Ratamuse/Open_beehive_scale_V0.2/Electronique balance/HTIT-WSL_V3.png

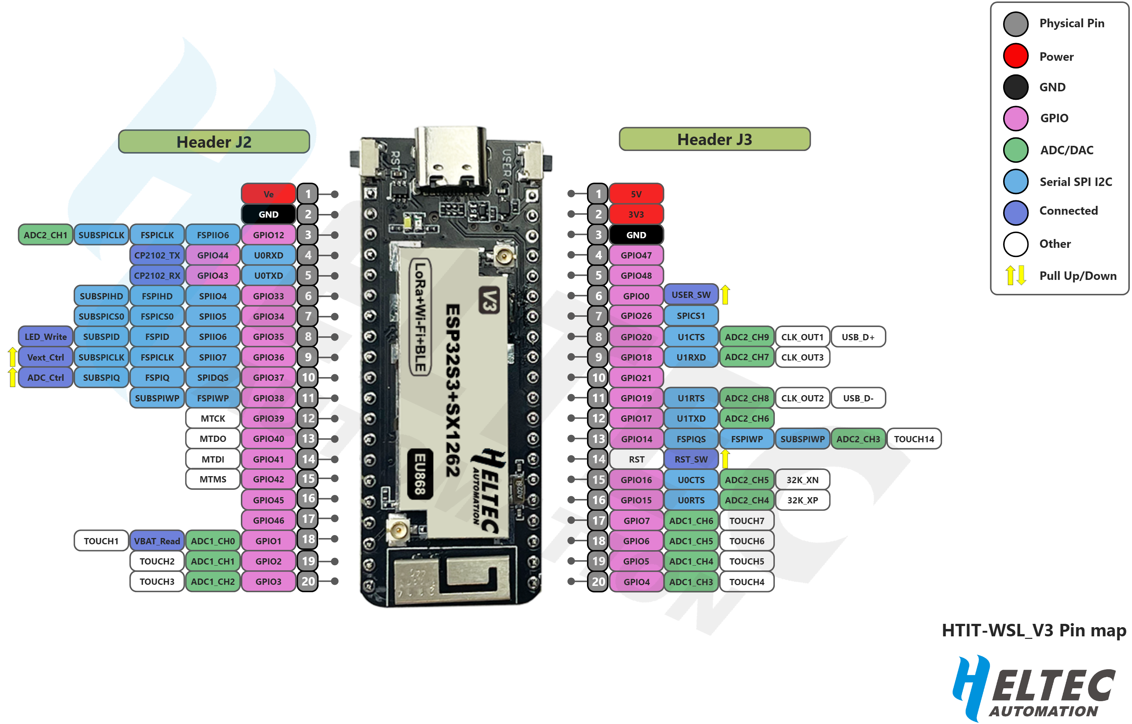
Electronique balance/HTIT-WSL_V3.png
