Ratamuse/Open_beehive_scale_V0.2/Electronique balance/3D/AO3400.stp

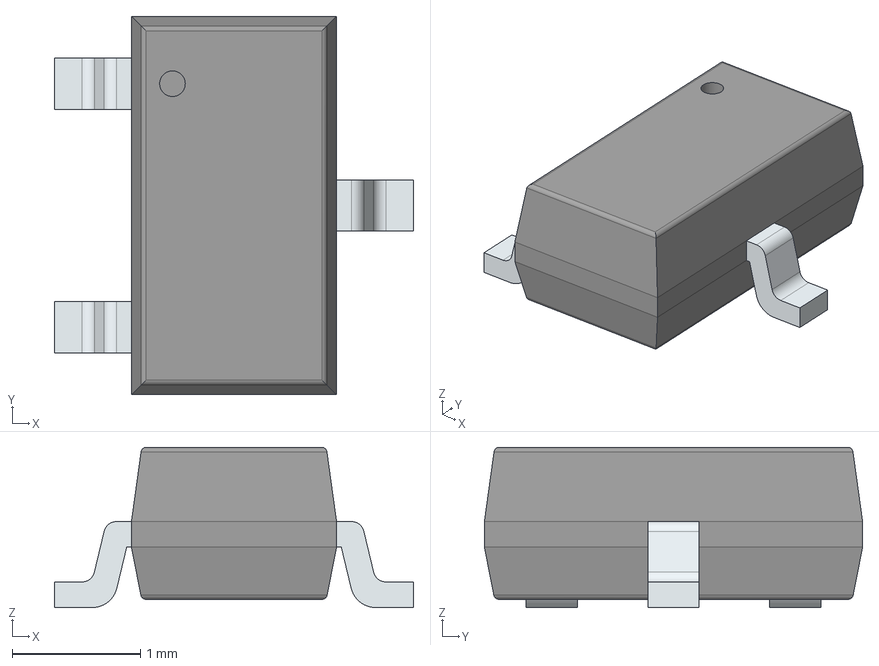
[picture p21: CAD file, 2022-06-07]
Electronique balance/3D/AO3400.stp
2.80 x 2.95 x 1.25 mm
PinsArrayL
FilletPinR
