Ratamuse/Open_beehive_scale_V0.2/Electronique balance/3D/FS8205.stp

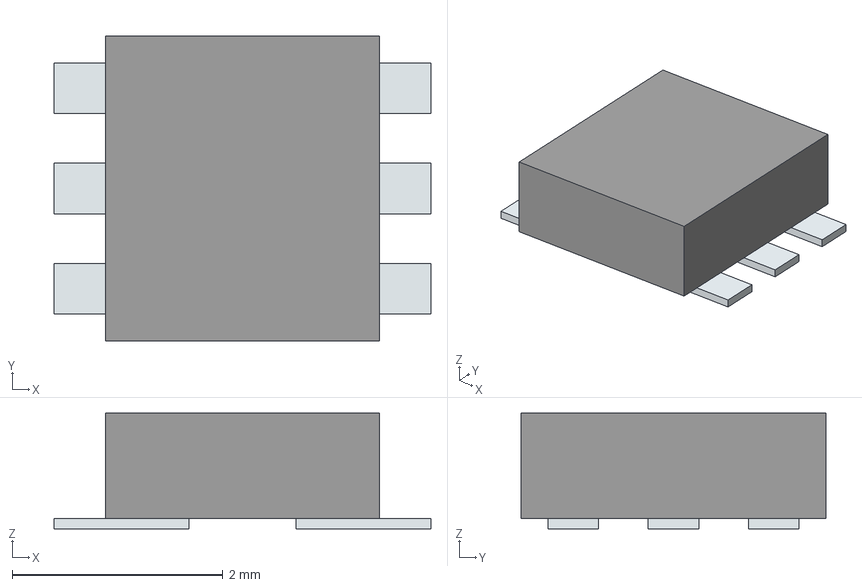
[picture p22: CAD file, 2022-06-07]
Electronique balance/3D/FS8205.stp
3.58 x 2.90 x 1.10 mm
Pins
