Ratamuse/Open_beehive_scale_V0.2/Electronique balance/3D/MMBT4403.stp

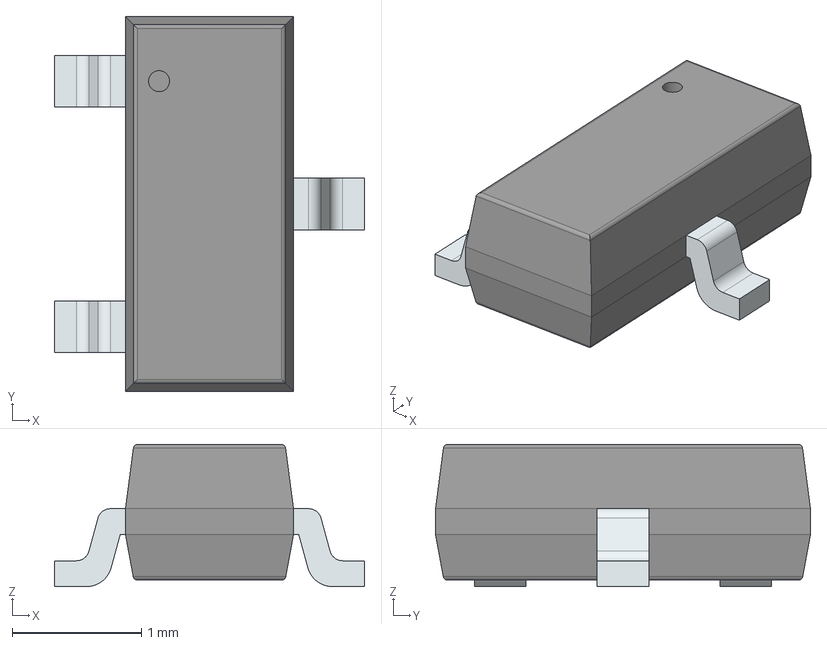
[picture p23: CAD file, 2022-06-07]
Electronique balance/3D/MMBT4403.stp
2.40 x 2.90 x 1.10 mm
PinsArrayL
FilletPinR
