Ratamuse/Open_beehive_scale_V0.2/Electronique balance/3D/B3S_100[].step

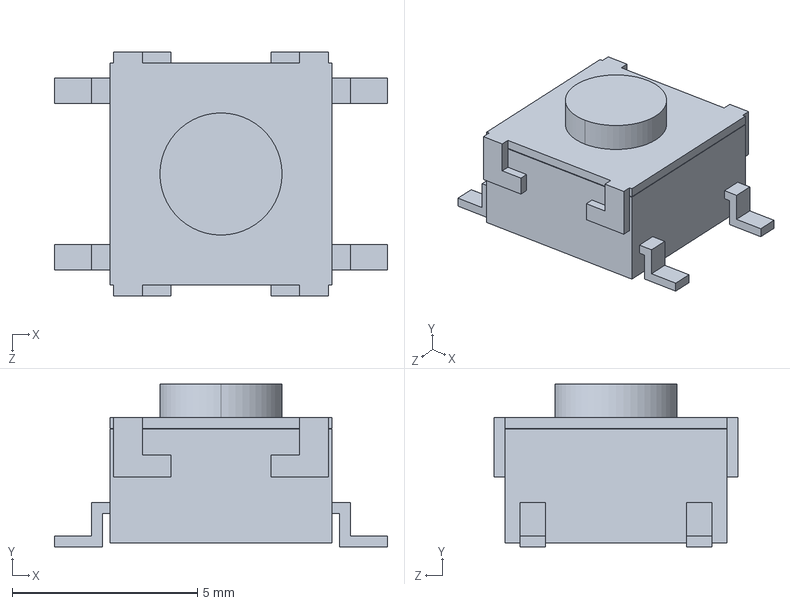
[picture p25: CAD file, 2022-06-07]
Electronique balance/3D/B3S_100[].step
9.00 x 4.40 x 6.60 mm
