Ratamuse/Open_beehive_scale_V0.2/Electronique balance/3D/SP1003-01DTG.stp

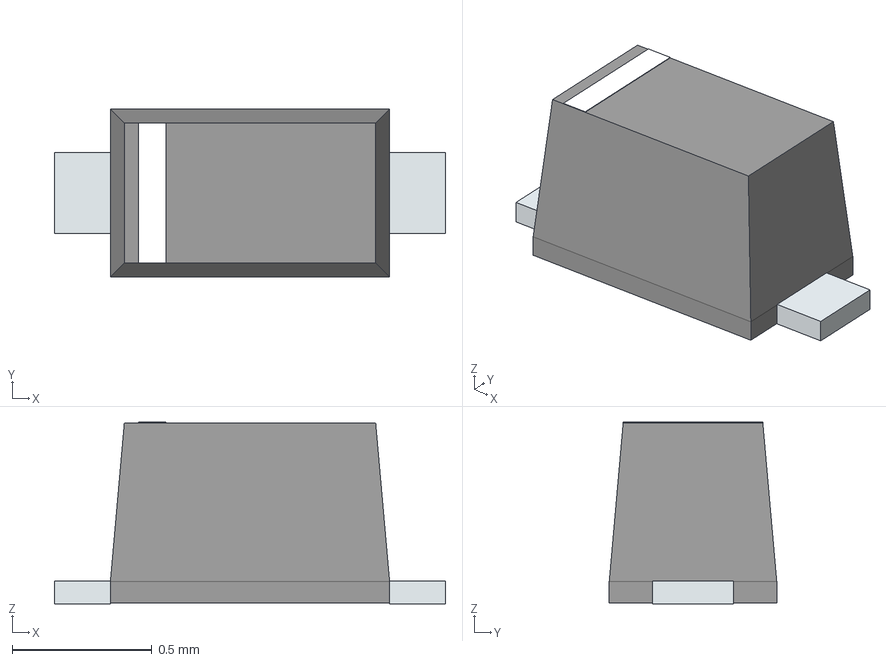
[picture p26: CAD file, 2022-06-07]
Electronique balance/3D/SP1003-01DTG.stp
1.40 x 0.6 x 0.65 mm
PinKIdent
PinK
PinA
