Ratamuse/Open_beehive_scale_V0.2/Electronique balance/3D/B4B-PH-SM4-TB.STEP

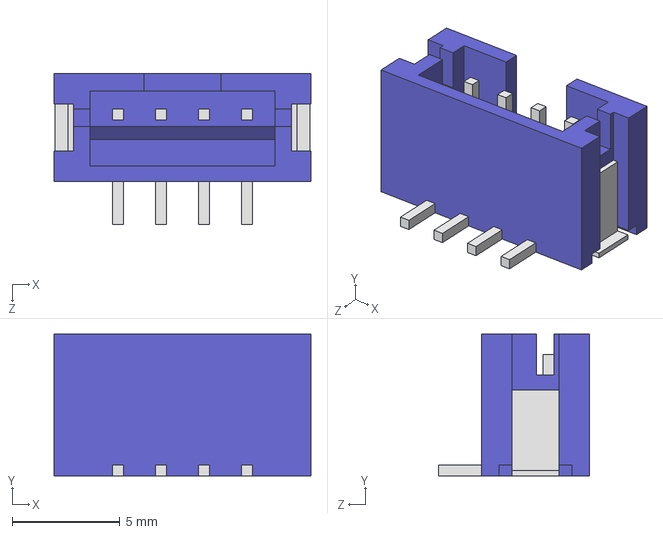
[picture p27: CAD file, 2022-06-07]
Electronique balance/3D/B4B-PH-SM4-TB.STEP
12.0 x 6.60 x 7.00 mm
