Ratamuse/Open_beehive_scale_V0.2/Electronique balance/3D/SdCard.stp

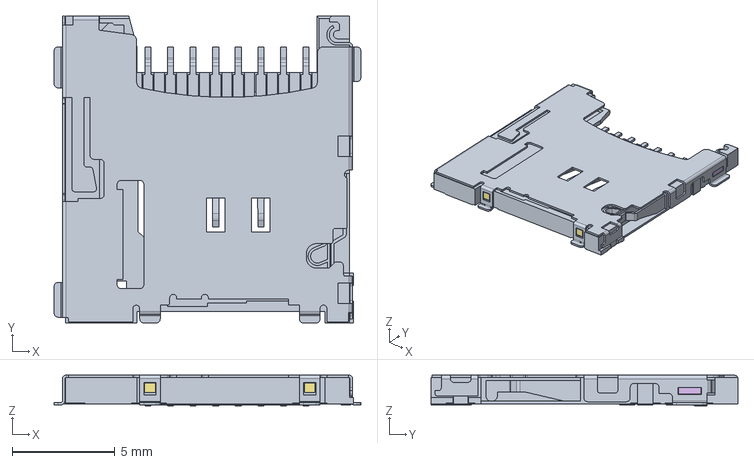
[picture p28: CAD file, 2022-06-07]
Electronique balance/3D/SdCard.stp
14.9 x 14.9 x 1.50 mm
