Ratamuse/Open_beehive_scale_V0.2/Electronique balance/3D/B2B-PH-K-S.STEP

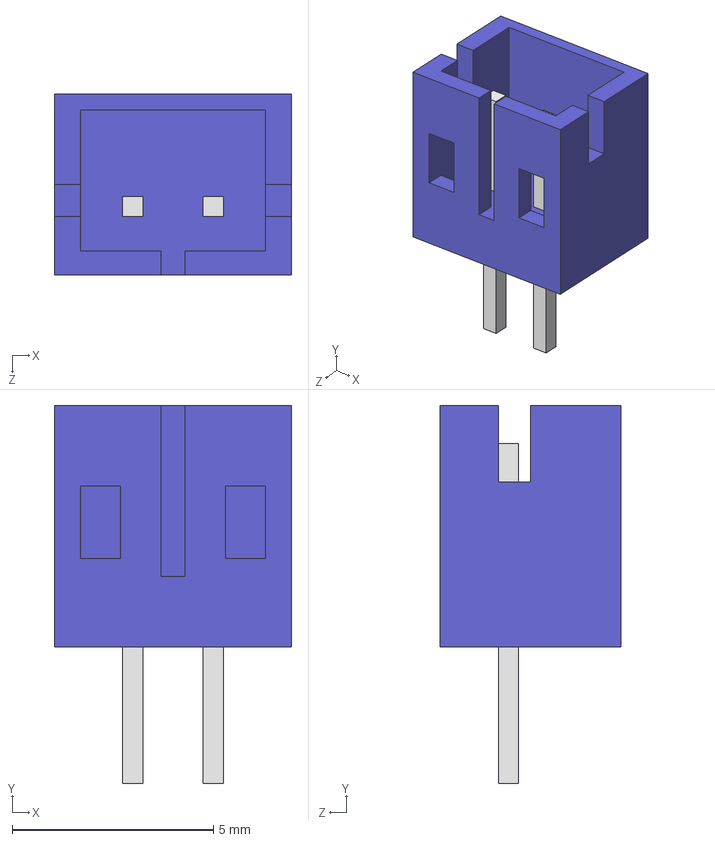
[picture p29: CAD file, 2022-06-07]
Electronique balance/3D/B2B-PH-K-S.STEP
5.90 x 9.40 x 4.50 mm
