Ratamuse/Open_beehive_scale_V0.2/Electronique balance/3D/HTSB-M3-8-5,5-1.STEP

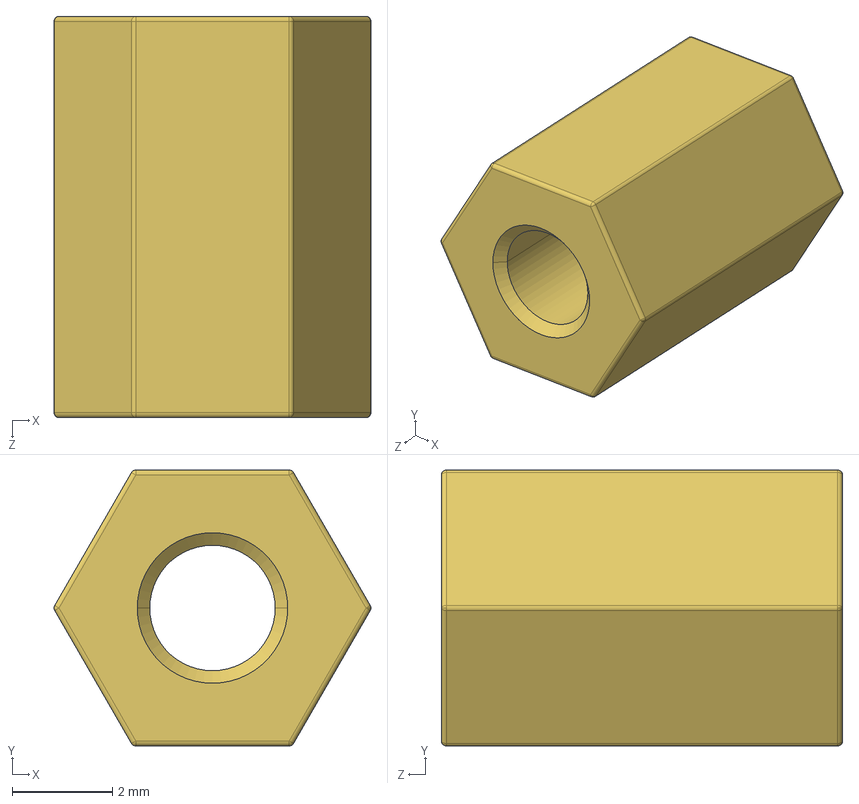
[picture p30: CAD file, 2022-06-07]
Electronique balance/3D/HTSB-M3-8-5,5-1.STEP
6.32 x 5.50 x 8.00 mm
