Ratamuse/Open_beehive_scale_V0.2/Electronique balance/3D/CN3791.stp

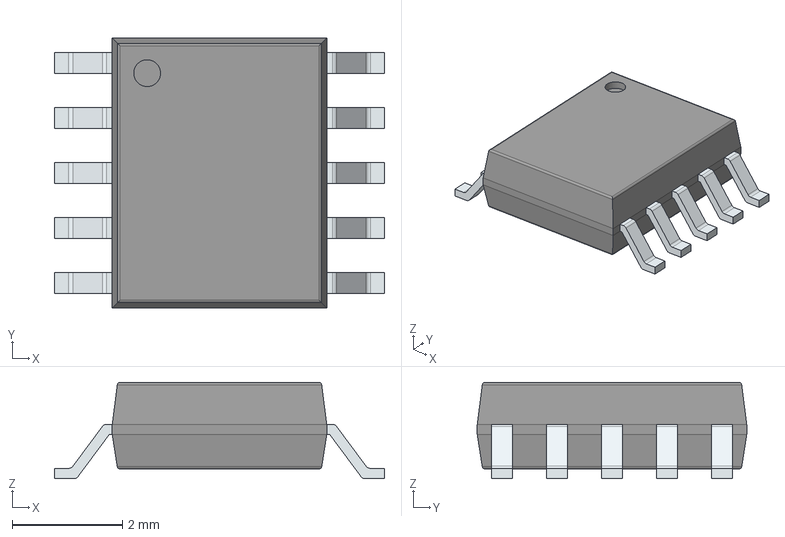
[picture p31: CAD file, 2022-06-07]
Electronique balance/3D/CN3791.stp
6.00 x 4.90 x 1.75 mm
PinsArrayLR
