Ratamuse/Open_beehive_scale_V0.2/Electronique balance/3D/PBS-14R.step

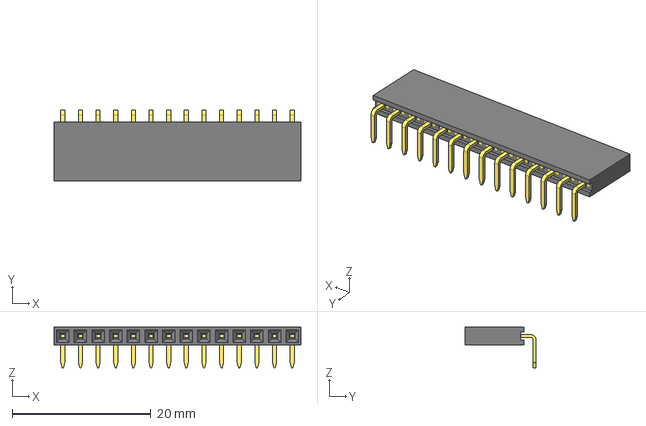
[picture p32: CAD file, 2022-06-07]
Electronique balance/3D/PBS-14R.step
35.6 x 10.2 x 5.84 mm
