Ratamuse/Open_beehive_scale_V0.2/Electronique balance/3D/FS8205A.stp

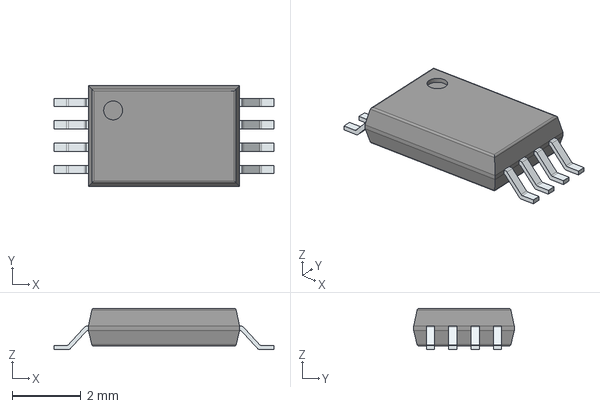
[picture p33: CAD file, 2022-06-07]
Electronique balance/3D/FS8205A.stp
6.40 x 2.93 x 1.20 mm
PinsArrayLR
