Ratamuse/Open_beehive_scale_V0.2/Electronique balance/3D/SHT41-AD1B-R3.stp

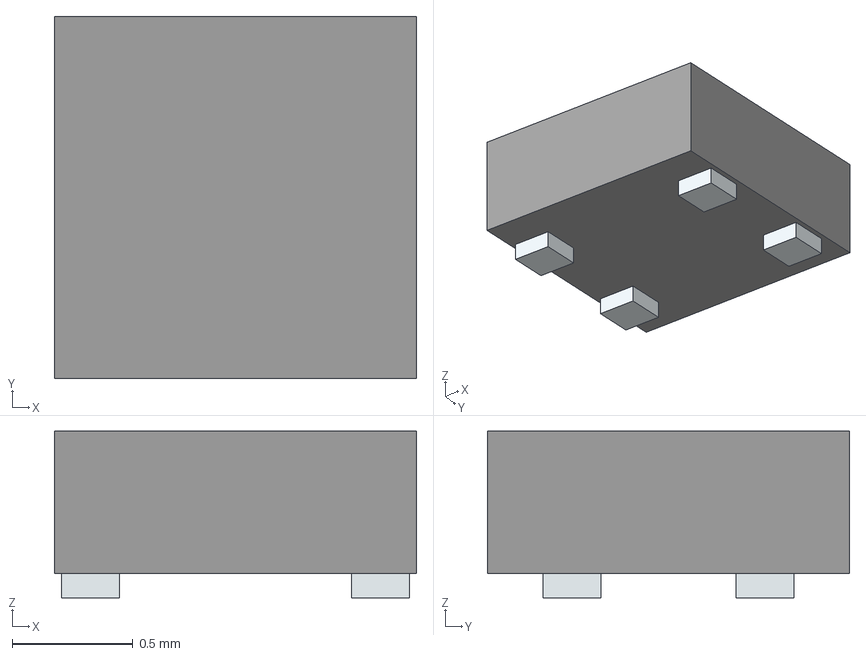
[picture p34: CAD file, 2022-06-07]
Electronique balance/3D/SHT41-AD1B-R3.stp
1.50 x 1.50 x 0.69 mm
Pins
