Ratamuse/Open_beehive_scale_V0.2/Electronique balance/3D/RB231X2.stp

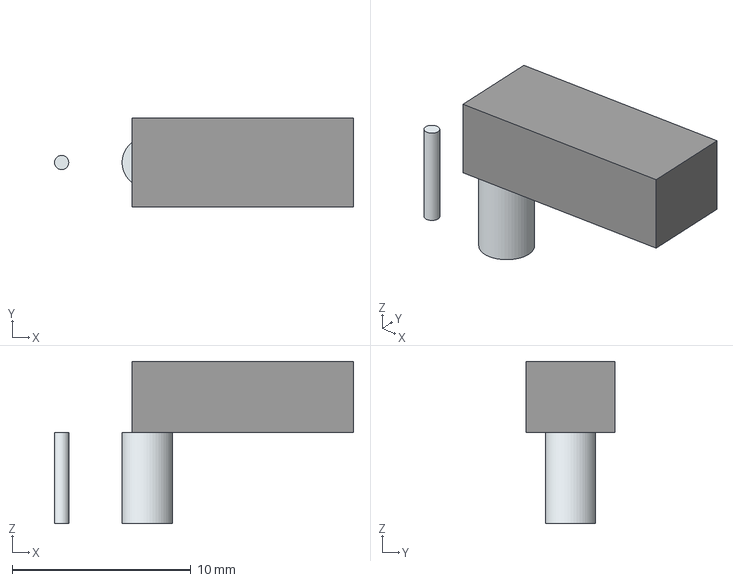
[picture p35: CAD file, 2022-06-07]
Electronique balance/3D/RB231X2.stp
16.7 x 5.00 x 9.10 mm
Leads x 2
