Ratamuse/Open_beehive_scale_V0.2/Electronique balance/3D/L86.step

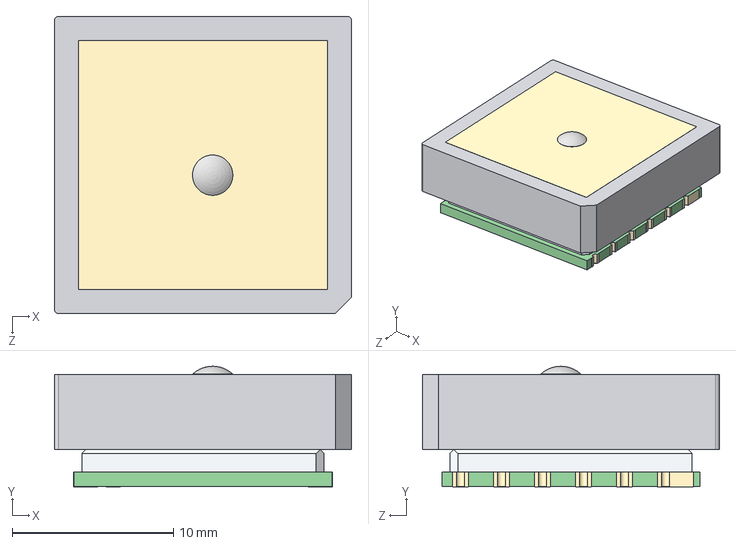
[picture p36: CAD file, 2022-06-07]
Electronique balance/3D/L86.step
18.4 x 7.47 x 18.4 mm
