Ratamuse/Open_beehive_scale_V0.2/Electronique balance/3D/XC6220B331MR-G.stp

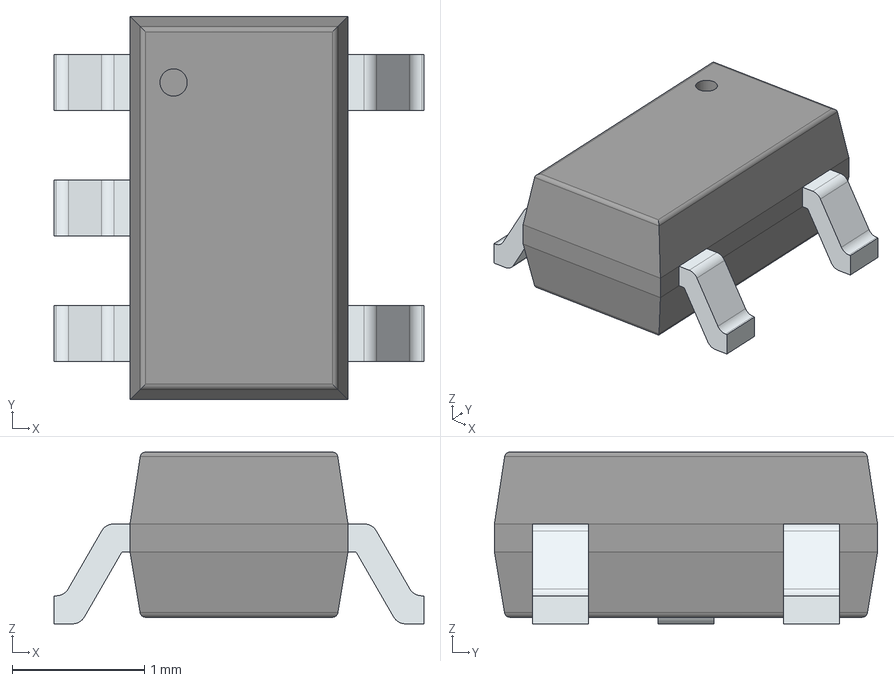
[picture p37: CAD file, 2022-06-07]
Electronique balance/3D/XC6220B331MR-G.stp
2.80 x 2.90 x 1.30 mm
PinsArrayL
PinsArrayR
