Ratamuse/Open_beehive_scale_V0.2/Electronique balance/3D/User Library-PC817_Gullwing.STEP

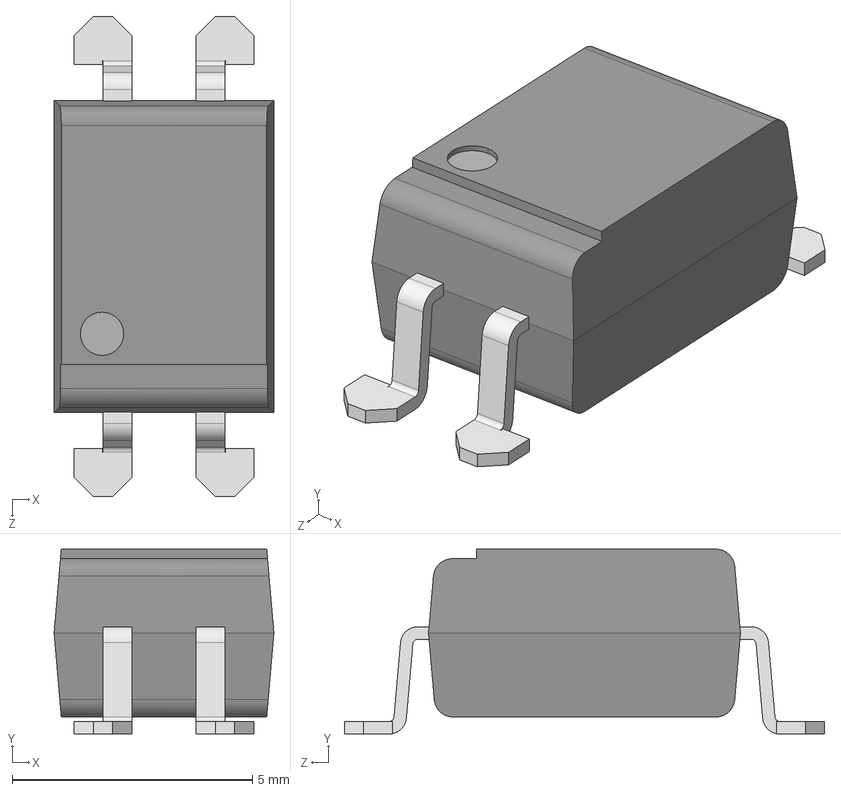
[picture p38: CAD file, 2022-06-07]
Electronique balance/3D/User Library-PC817_Gullwing.STEP
4.58 x 3.85 x 10.0 mm
PC817 Body
Gullwing Pin
Gullwing Pin_MIR
Gullwing Pin_MIR1
Gullwing Pin_MIR_MIR
