Ratamuse/Open_beehive_scale_V0.2/Electronique balance/3D/HX711.stp

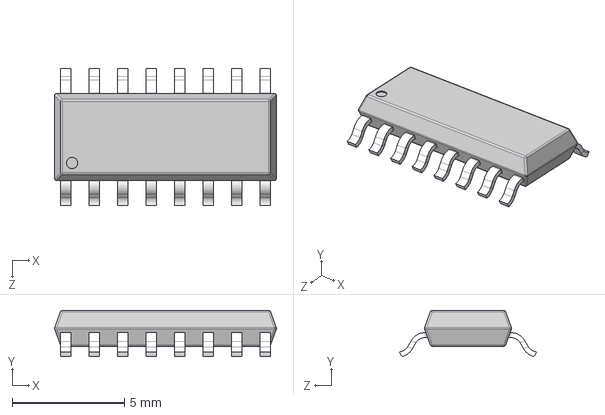
[picture p39: CAD file, 2022-06-07]
Electronique balance/3D/HX711.stp
9.89 x 2.05 x 6.12 mm
