Ratamuse/Open_beehive_scale_V0.2/Electronique balance/3D/SS34.stp

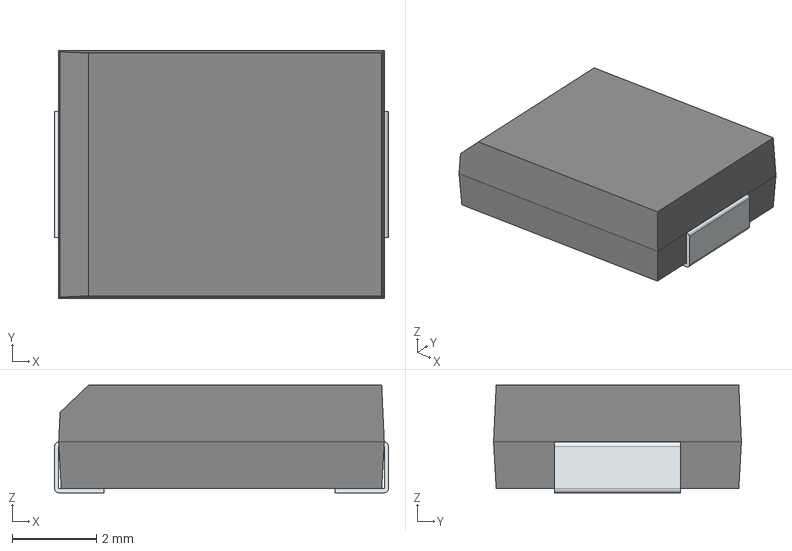
[picture p40: CAD file, 2022-06-07]
Electronique balance/3D/SS34.stp
7.95 x 5.90 x 2.56 mm
FilletPin1
FilletPin2
