Ratamuse/Open_beehive_scale_V0.2/Electronique balance/3D/BME680.step

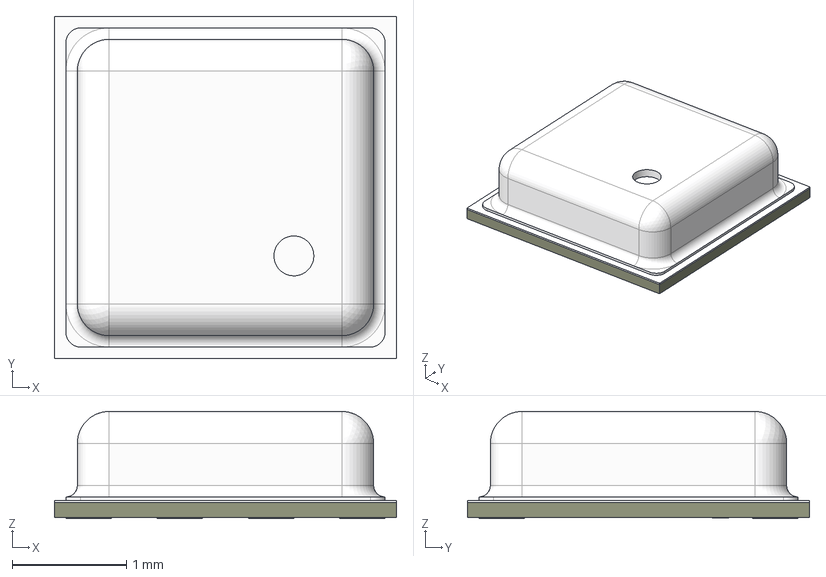
[picture p42: CAD file, 2022-06-07]
Electronique balance/3D/BME680.step
3.00 x 3.00 x 0.94 mm
pads
pcb
lid
