Ratamuse/Open_beehive_scale_V0.2/Electronique balance/3D/PTS636SL43SMTRLFS.stp

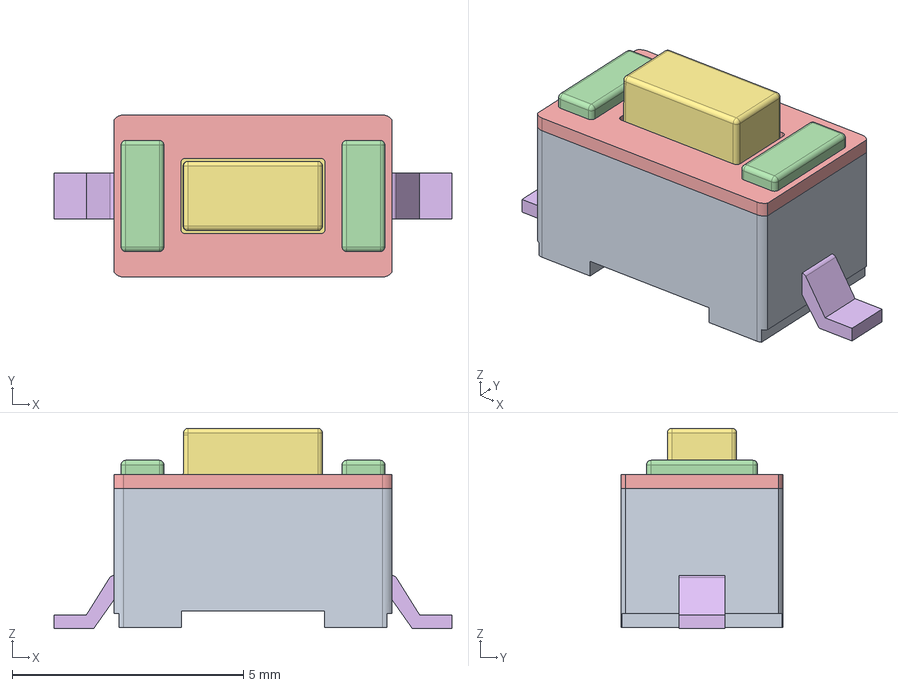
[picture p43: CAD file, 2022-06-07]
Electronique balance/3D/PTS636SL43SMTRLFS.stp
8.60 x 3.50 x 4.33 mm
