Ratamuse/Open_beehive_scale_V0.2/Electronique balance/3D/HTSB-M3-12-5-1.STEP

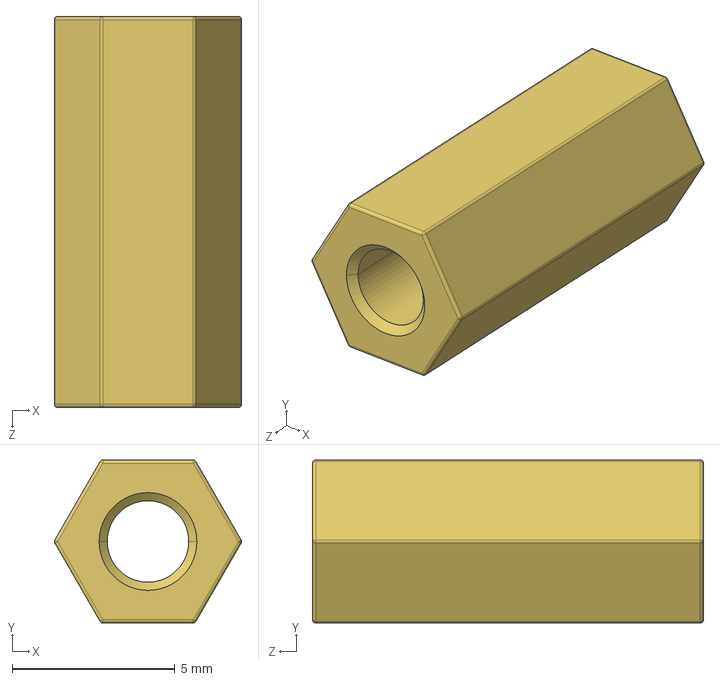
[picture p44: CAD file, 2022-06-07]
Electronique balance/3D/HTSB-M3-12-5-1.STEP
5.74 x 5.00 x 12.0 mm
