Ratamuse/Open_beehive_scale_V0.2/Electronique balance/3D/connecteurs5.stp

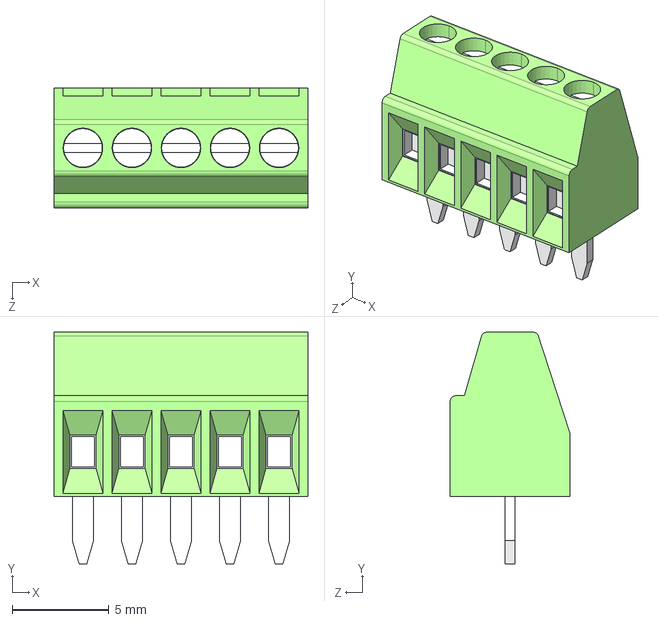
[picture p45: CAD file, 2022-06-07]
Electronique balance/3D/connecteurs5.stp
13.2 x 12.0 x 6.20 mm
