Ratamuse/Open_beehive_scale_V0.2/Electronique balance/3D/12BHC186P1-GR.stp

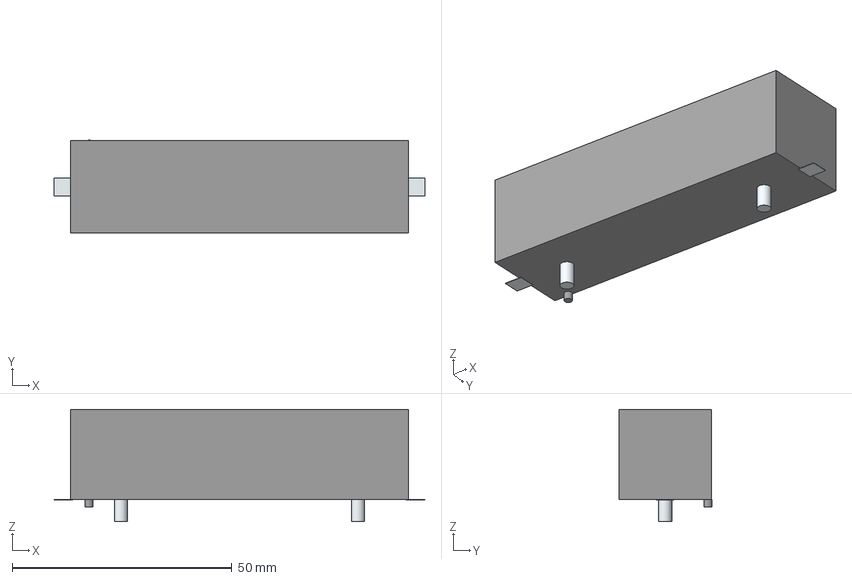
[picture p46: CAD file, 2022-06-07]
Electronique balance/3D/12BHC186P1-GR.stp
84.5 x 21.1 x 25.6 mm
Pins
Lugs x 3
Leads x 3
