Ratamuse/Open_beehive_scale_V0.2/Electronique balance/3D/FS312F-G.stp

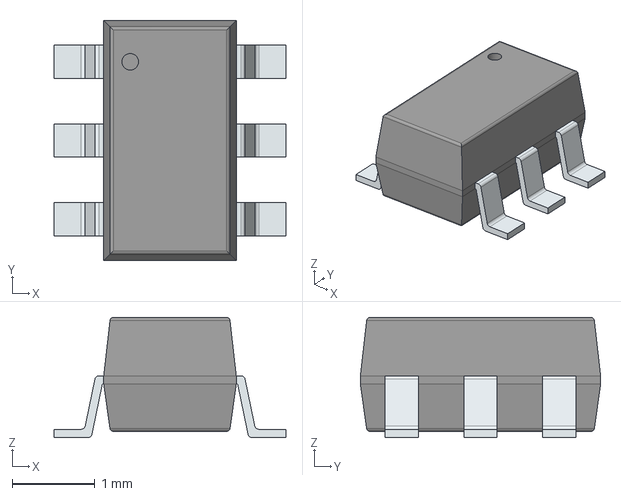
[picture p47: CAD file, 2022-06-07]
Electronique balance/3D/FS312F-G.stp
2.80 x 2.90 x 1.45 mm
PinsArrayLR
